jeremynguyenn/Vehicle-Control-Unit-hardware-and-firmware/VCU2_firmware/Core/Src/adc.c

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
/* Includes ------------------------------------------------------------------*/
#include "adc.h"

/* USER CODE BEGIN 0 */
#include <assert.h>

volatile uint32_t Sensor_DMABase[NUM_ADC_CHANNELS] = {0};


/* USER CODE END 0 */

ADC_HandleTypeDef hadc1;
DMA_HandleTypeDef hdma_adc1;

/* ADC1 init function */
void MX_ADC1_Init(void)
{

  ADC_ChannelConfTypeDef sConfig = {0};

  /** Configure the global features of the ADC (Clock, Resolution, Data Alignment and number of conversion)
  */
  hadc1.Instance = ADC1;
  hadc1.Init.ClockPrescaler = ADC_CLOCK_SYNC_PCLK_DIV2;
  hadc1.Init.Resolution = ADC_RESOLUTION_12B;
  hadc1.Init.ScanConvMode = ENABLE;
  hadc1.Init.ContinuousConvMode = ENABLE;
  hadc1.Init.DiscontinuousConvMode = DISABLE;
  hadc1.Init.ExternalTrigConvEdge = ADC_EXTERNALTRIGCONVEDGE_NONE;
  hadc1.Init.ExternalTrigConv = ADC_SOFTWARE_START;
  hadc1.Init.DataAlign = ADC_DATAALIGN_RIGHT;
  hadc1.Init.NbrOfConversion = 3;
  hadc1.Init.DMAContinuousRequests = ENABLE;
  hadc1.Init.EOCSelection = ADC_EOC_SINGLE_CONV;
  if (HAL_ADC_Init(&hadc1) != HAL_OK)
  {
    Error_Handler();
  }

  /** Configure for the selected ADC regular channel its corresponding rank in the sequencer and its sample time.
  */
  sConfig.Channel = ADC_CHANNEL_10;
  sConfig.Rank = 1;
  sConfig.SamplingTime = ADC_SAMPLETIME_144CYCLES;
  if (HAL_ADC_ConfigChannel(&hadc1, &sConfig) != HAL_OK)
  {
    Error_Handler();
  }

  /** Configure for the selected ADC regular channel its corresponding rank in the sequencer and its sample time.
  */
  sConfig.Channel = ADC_CHANNEL_5;
  sConfig.Rank = 2;
  if (HAL_ADC_ConfigChannel(&hadc1, &sConfig) != HAL_OK)
  {
    Error_Handler();
  }

  /** Configure for the selected ADC regular channel its corresponding rank in the sequencer and its sample time.
  */
  sConfig.Channel = ADC_CHANNEL_7;
  sConfig.Rank = 3;
  if (HAL_ADC_ConfigChannel(&hadc1, &sConfig) != HAL_OK)
  {
    Error_Handler();
  }
  /* USER CODE BEGIN ADC1_Init 2 */
  HAL_ADC_MspInit(&hadc1);
  HAL_ADC_Start_DMA(&hadc1, (uint32_t*) Sensor_DMABase, NUM_ADC_CHANNELS);
  /* USER CODE END ADC1_Init 2 */

}

void HAL_ADC_MspInit(ADC_HandleTypeDef* adcHandle)
{

  GPIO_InitTypeDef GPIO_InitStruct = {0};
  if(adcHandle->Instance==ADC1)
  {
    /* ADC1 clock enable */
    __HAL_RCC_ADC1_CLK_ENABLE();

    __HAL_RCC_GPIOC_CLK_ENABLE();
    __HAL_RCC_GPIOA_CLK_ENABLE();
    /**ADC1 GPIO Configuration
    PC0     ------> ADC1_IN10
    PA5     ------> ADC1_IN5
    PA7     ------> ADC1_IN7
    */
    GPIO_InitStruct.Pin = APPS1_Pin;
    GPIO_InitStruct.Mode = GPIO_MODE_ANALOG;
    GPIO_InitStruct.Pull = GPIO_NOPULL;
    HAL_GPIO_Init(APPS1_GPIO_Port, &GPIO_InitStruct);

    GPIO_InitStruct.Pin = APPS2_Pin|VBATT_Pin;
    GPIO_InitStruct.Mode = GPIO_MODE_ANALOG;
    GPIO_InitStruct.Pull = GPIO_NOPULL;
    HAL_GPIO_Init(GPIOA, &GPIO_InitStruct);

    /* ADC1 DMA Init */
    /* ADC1 Init */
    hdma_adc1.Instance = DMA2_Stream0;
    hdma_adc1.Init.Channel = DMA_CHANNEL_0;
    hdma_adc1.Init.Direction = DMA_PERIPH_TO_MEMORY;
    hdma_adc1.Init.PeriphInc = DMA_PINC_DISABLE;
    hdma_adc1.Init.MemInc = DMA_MINC_ENABLE;
    hdma_adc1.Init.PeriphDataAlignment = DMA_PDATAALIGN_WORD;
    hdma_adc1.Init.MemDataAlignment = DMA_MDATAALIGN_WORD;
    hdma_adc1.Init.Mode = DMA_CIRCULAR;
    hdma_adc1.Init.Priority = DMA_PRIORITY_HIGH;
    hdma_adc1.Init.FIFOMode = DMA_FIFOMODE_ENABLE;
    hdma_adc1.Init.FIFOThreshold = DMA_FIFO_THRESHOLD_FULL;
    hdma_adc1.Init.MemBurst = DMA_MBURST_SINGLE;
    hdma_adc1.Init.PeriphBurst = DMA_PBURST_SINGLE;
    if (HAL_DMA_Init(&hdma_adc1) != HAL_OK)
    {
      Error_Handler();
    }

    __HAL_LINKDMA(adcHandle,DMA_Handle,hdma_adc1);

  }
}

void HAL_ADC_MspDeInit(ADC_HandleTypeDef* adcHandle)
{

  if(adcHandle->Instance==ADC1)
  {
    /* Peripheral clock disable */
    __HAL_RCC_ADC1_CLK_DISABLE();

    /**ADC1 GPIO Configuration
    PC0     ------> ADC1_IN10
    PA5     ------> ADC1_IN5
    PA7     ------> ADC1_IN7
    */
    HAL_GPIO_DeInit(APPS1_GPIO_Port, APPS1_Pin);

    HAL_GPIO_DeInit(GPIOA, APPS2_Pin|VBATT_Pin);

    /* ADC1 DMA DeInit */
    HAL_DMA_DeInit(adcHandle->DMA_Handle);
  }
}

/* USER CODE BEGIN 1 */

/*
 * ADC_get_val
 *
 * @Brief: This function is used to get a measured ADC value
 * @Param item: The item to get. Should be one of @ADC Vals
 * @Return: returns the most recent conversion of the given value. on failure returns 0
 */
uint32_t ADC_get_val(uint8_t item){
    uint32_t retVal = INVALID_ADC_READING;
    if(item < NUM_ADC_CHANNELS){// && HAL_DMA_PollForTransfer(&hdma_adc1, HAL_DMA_FULL_TRANSFER, 100)){
        retVal = Sensor_DMABase[item];
    }
    return retVal;
}

// adc_convert() is for if you wanted one sample and
// had something against the "nice" DMA I(bouchard) set up....
uint32_t adc_convert(){
    HAL_ADC_Start(&hadc1);//Start the conversion
    while(!__HAL_ADC_GET_FLAG(&hadc1, ADC_FLAG_EOC));//Processing the conversion
    return HAL_ADC_GetValue(&hadc1); //Return the converted data
}

/* USER CODE END 1 */
