jeremynguyenn/Vehicle-Control-Unit-hardware-and-firmware/VCU2_firmware/Core/Src/usart.c

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
/* Includes ------------------------------------------------------------------*/
#include "usart.h"

USART_HandleTypeDef husart2;

/* USART2 init function */
void MX_USART2_Init(void)
{

  husart2.Instance = USART2;
  husart2.Init.BaudRate = 115200;
  husart2.Init.WordLength = USART_WORDLENGTH_8B;
  husart2.Init.StopBits = USART_STOPBITS_1;
  husart2.Init.Parity = USART_PARITY_NONE;
  husart2.Init.Mode = USART_MODE_TX_RX;
  husart2.Init.CLKPolarity = USART_POLARITY_LOW;
  husart2.Init.CLKPhase = USART_PHASE_1EDGE;
  husart2.Init.CLKLastBit = USART_LASTBIT_DISABLE;
  if (HAL_USART_Init(&husart2) != HAL_OK)
  {
    Error_Handler();
  }
}

void HAL_USART_MspInit(USART_HandleTypeDef* usartHandle)
{

  GPIO_InitTypeDef GPIO_InitStruct = {0};
  if(usartHandle->Instance==USART2)
  {
    /* USART2 clock enable */
    __HAL_RCC_USART2_CLK_ENABLE();

    __HAL_RCC_GPIOA_CLK_ENABLE();
    /**USART2 GPIO Configuration
    PA2     ------> USART2_TX
    PA3     ------> USART2_RX
    PA4     ------> USART2_CK
    */
    GPIO_InitStruct.Pin = GPIO_PIN_2|GPIO_PIN_3|GPIO_PIN_4;
    GPIO_InitStruct.Mode = GPIO_MODE_AF_PP;
    GPIO_InitStruct.Pull = GPIO_NOPULL;
    GPIO_InitStruct.Speed = GPIO_SPEED_FREQ_VERY_HIGH;
    GPIO_InitStruct.Alternate = GPIO_AF7_USART2;
    HAL_GPIO_Init(GPIOA, &GPIO_InitStruct);

  }
}

void HAL_USART_MspDeInit(USART_HandleTypeDef* usartHandle)
{

  if(usartHandle->Instance==USART2)
  {
    /* Peripheral clock disable */
    __HAL_RCC_USART2_CLK_DISABLE();

    /**USART2 GPIO Configuration
    PA2     ------> USART2_TX
    PA3     ------> USART2_RX
    PA4     ------> USART2_CK
    */
    HAL_GPIO_DeInit(GPIOA, GPIO_PIN_2|GPIO_PIN_3|GPIO_PIN_4);

  }
}

/* USER CODE BEGIN 1 */
//TODO Bluetooth
//uint8_t usartBTSend( char * Data){
//    BaseType_t retRTOS = 0;
//    uint32_t ulNotifiedValue;
//    uint8_t ret = 0;
//    uint32_t count = 0;
//    retRTOS = xSemaphoreTake( BLUTOOTH_USART.sem,  pdMS_TO_TICKS(USART_TIMEOUT));
//    if(retRTOS == pdPASS){
//        BLUTOOTH_USART.printHandle = xTaskGetCurrentTaskHandle();
//        //USARTx->curPrintingTask = xTaskGetCurrentTaskHandle();
//        bool end = false;
//        while(!end){
//            if(Data[count] == BT_END_FLAG) {
//                end = true;
//            }
//            USART_SendData(BLUTOOTH_USART.usart, Data[count]);
//            count++;
//
//            if(BLUTOOTH_USART.usart == USART3){
//                BLUTOOTH_USART.txEnabled = true;
//            }
//            USART_ITConfig(BLUTOOTH_USART.usart, USART_IT_TXE, ENABLE);
//
//            retRTOS = xTaskNotifyWait(0x00,0x00, &ulNotifiedValue, pdMS_TO_TICKS(USART_TIMEOUT));
//            //check if timeout
//            if(retRTOS != pdTRUE){
//                ret = 1;
//            }
//        }
//        xSemaphoreGive(BLUTOOTH_USART.sem);
//    }
//    else{
//        ret = 1;
//    }
//    return ret;
//}

/* USER CODE END 1 */
