jeremynguyenn/Vehicle-Control-Unit-hardware-and-firmware/VCU2_firmware/Core/Inc/iwdg.h

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
/* Define to prevent recursive inclusion -------------------------------------*/
#ifndef __IWDG_H__
#define __IWDG_H__

#ifdef __cplusplus
extern "C" {
#endif

/* Includes ------------------------------------------------------------------*/
#include "main.h"

/* USER CODE BEGIN Includes */
#include <stdbool.h>
#include "cmsis_os2.h"
/* USER CODE END Includes */

extern IWDG_HandleTypeDef hiwdg;

void MX_IWDG_Init(void);

/* USER CODE BEGIN Prototypes */
typedef struct {
    const osThreadId_t* taskHandle;
    uint8_t isTaskActive;
} TaskInfo;

typedef enum {
    DEFAULT_TASK,
    DASH_LED_TASK,
    WATCH_DOG_TASK,
    CAN_TX_TASK,
    CAN_RX_TASK,
    BT_DUMP_TASK,
    VCU_STATE_TASK,
    MC_HRTBEAT_TASK,
    ACU_HRTBEAT_TASK,
    APPS_PROC_TASK,
    MC_CAN_COMMS_TASK,
    ACU_CAN_COMMS_TASK,
    NUM_TASKS
} TaskBit_t;

bool startFromIWDG();
extern osEventFlagsId_t iwdgEventGroupHandle;
void kickWatchdogBit(osThreadId_t taskHandle);
/* USER CODE END Prototypes */

#ifdef __cplusplus
}
#endif

#endif /* __IWDG_H__ */
