jeremynguyenn/Vehicle-Control-Unit-hardware-and-firmware/VCU2_firmware/Core/Inc/mc_comms_handler.h

/*
 * mc_comms_handler.h
 *
 *  Created on: Apr 27, 2024
 *      Author: tonyz
 */

#ifndef INC_MC_COMMS_HANDLER_H_
#define INC_MC_COMMS_HANDLER_H_

void notify_mc_heartbeat_task();


#endif /* INC_MC_COMMS_HANDLER_H_ */
