jeremynguyenn/Vehicle-Control-Unit-hardware-and-firmware/VCU2_firmware/Core/Inc/startup_condition.h

/*
 * startup_condition.h
 *
 *  Created on: Dec 27, 2018
 *      Author: Martin Rickey
 */

#ifndef STARTUP_CONDITION_H_
#define STARTUP_CONDITION_H_

void checkStartupCondition();

#endif /* STARTUP_CONDITION_H_ */
