jeremynguyenn/Vehicle-Control-Unit-hardware-and-firmware/VCU2_firmware/Core/Inc/vcu_startup.h

#ifndef VCU_STARTUP_H
#define VCU_STARTUP_H
#include "FreeRTOS.h"
#include "task.h"
#include "cmsis_os2.h"

void go_idle();
int checkHeartbeat();
void goTSA();
void goRTD();
TaskHandle_t get_startup_task();

enum startup_notify_value{
	ACU_TSA_NACK = 0,
	ACU_TSA_ACK,
	ACU_RTD_NACK,
	ACU_RTD_ACK,
	GO_IDLE_REQ_FROM_ACU
};

enum safetyLoopState{
    SAFETY_LOOP_OPEN = 0,
    SAFETY_LOOP_CLOSED
};

void set_safety_loop_state(enum safetyLoopState state); //use this for blocking the safety loop in scary conditions
bool read_saftey_loop();

#endif
